mvw123/EMF_Sensor/EMF_Receiver.sch

## KiCad design EMF_Receiver.sch (2014-07-28, an earlier design)

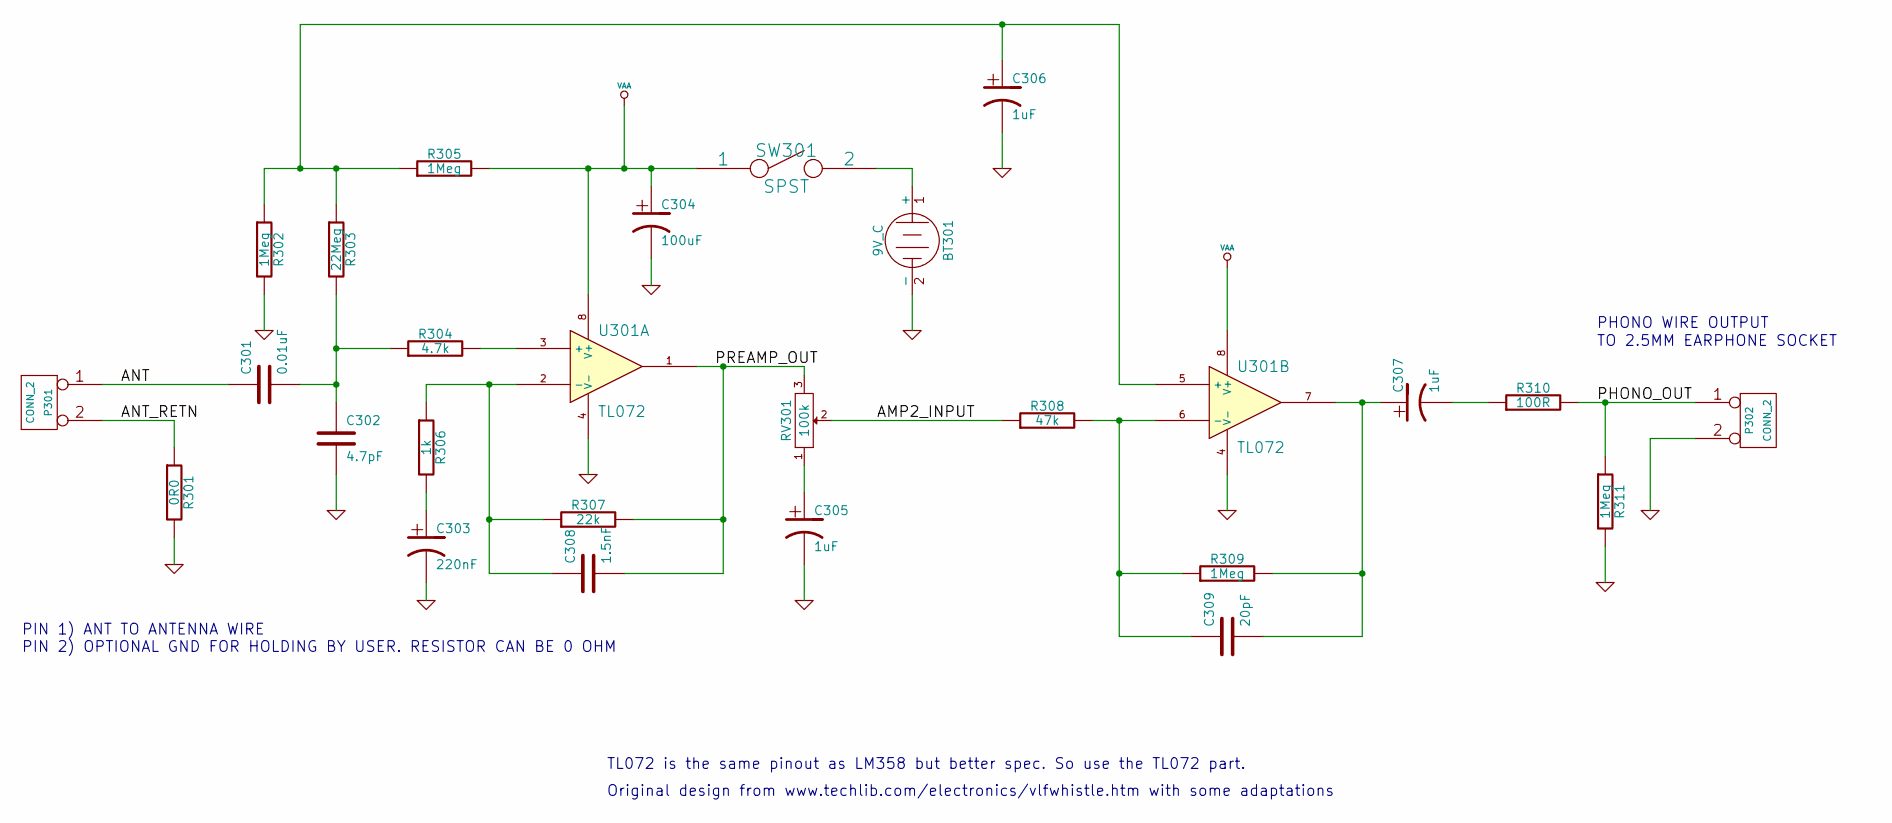
[picture p10: schematic EMF_Receiver.sch]

Parts:
BT301: 9V_C
C301: 0.01uF
C302: 4.7pF
C303: 220nF
C304: 100uF
C305, C306, C307: 1uF
C308: 1.5nF
C309: 20pF
P301, P302: CONN_2
R301: 0R0
R302, R305, R309, R311: 1Meg
R303: 22Meg
R304: 4.7k
R306: 1k
R307: 22k
R308: 47k
R310: 100R
RV301: 100k
SW301: SPST
U301: TL072

Connections:
AMP2_INPUT: R308.1, RV301.2
ANT: C301.1, P301.1
ANT_RETN: P301.2 (PM), R301.1
GND: BT301.2 (-), C302.2, C303.2, C304.2, C305.2, C306.2, P302.2 (PM), R301.2, R302.2, R311.2, U301.4 (V-)
unnamed: BT301.1 (+), SW301.2
unnamed: C301.2, C302.1, R303.2, R304.1
unnamed: C303.1, R306.2
unnamed: C305.1, RV301.1
unnamed: C306.1, R302.1, R303.1, R305.1, U301.5 (+)
unnamed: C307.1, C309.2, R309.2, U301.7
unnamed: C307.2, R310.1
unnamed: C308.1, R306.1, R307.1, U301.2 (-)
unnamed: C309.1, R308.2, R309.1, U301.6 (-)
unnamed: R304.2, U301.3 (+)
PHONO_OUT: P302.1, R310.2, R311.1
PREAMP_OUT: C308.2, R307.2, RV301.3, U301.1
VAA: C304.1, R305.2, SW301.1, U301.8 (V+)

Notes on the sheet:
PHONO WIRE OUTPUT
TO 2.5MM EARPHONE SOCKET
PIN 1) ANT TO ANTENNA WIRE PIN 2) OPTIONAL GND FOR HOLDING BY USER. RESISTOR CAN BE 0 OHM
Original design from www.techlib.com/electronics/vlfwhistle.htm with some adaptations
TL072 is the same pinout as LM358 but better spec. So use the TL072 part.
