mvw123/EMF_Sensor/RelaxationOscillator.sch

## KiCad design RelaxationOscillator.sch (2014-07-28, an earlier design)

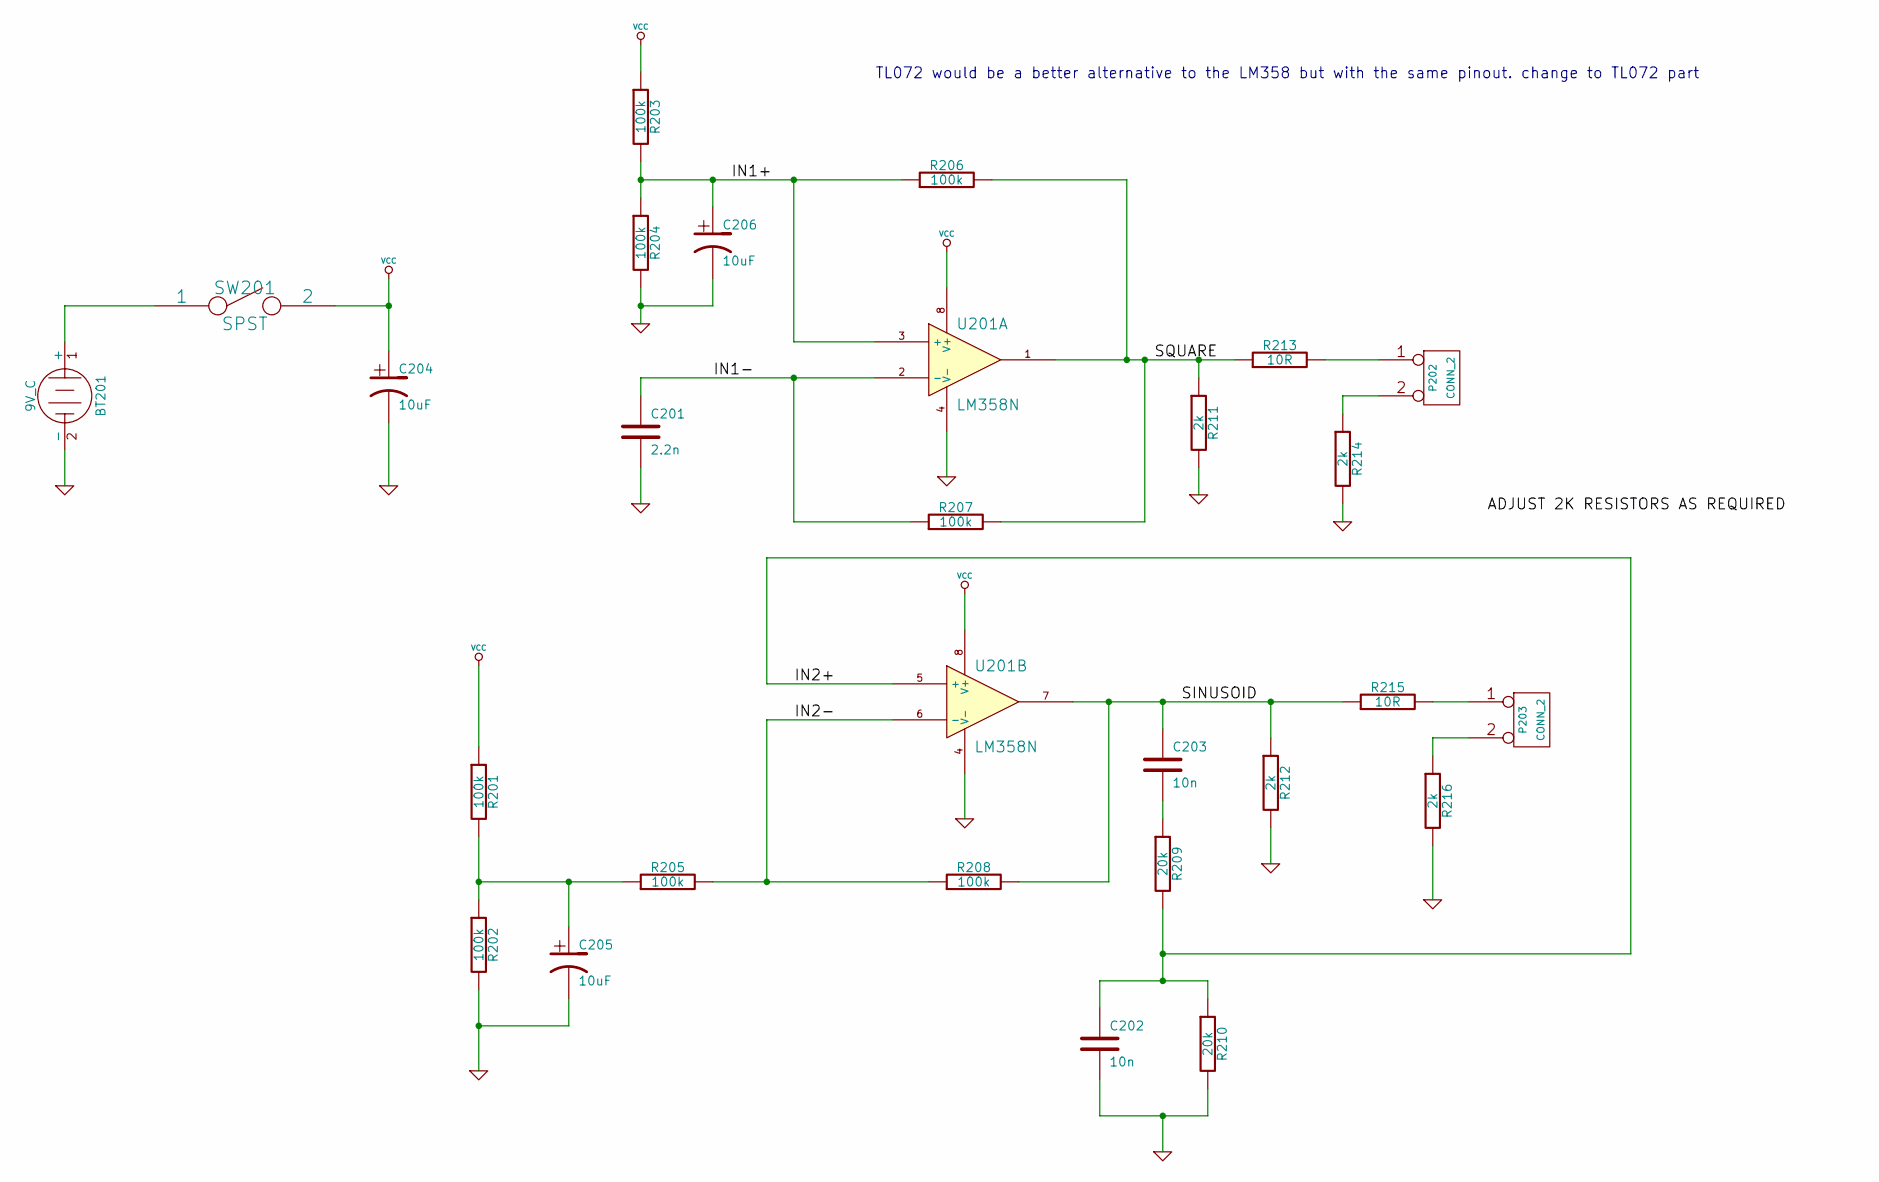
[picture p11: schematic RelaxationOscillator.sch]

Parts:
BT201: 9V_C
C201: 2.2n
C202, C203: 10n
C204, C205, C206: 10uF
P202, P203: CONN_2
R201, R202, R203, R204, R205, R206, R207, R208: 100k
R209, R210: 20k
R211, R212, R214, R216: 2k
R213, R215: 10R
SW201: SPST
U201: LM358N

Connections:
GND: BT201.2 (-), C201.2, C202.2, C204.2, C205.2, C206.2, R202.2, R204.2, R210.2, R211.2, R212.2, R214.2, R216.2, U201.4 (V-)
IN1+: C206.1, R203.2, R204.1, R206.1, U201.3 (+)
IN1-: C201.1, R207.1, U201.2 (-)
IN2+: C202.1, R209.2, R210.1, U201.5 (+)
IN2-: R205.2, R208.1, U201.6 (-)
unnamed: BT201.1 (+), SW201.1
unnamed: C203.2, R209.1
unnamed: C205.1, R201.2, R202.1, R205.1
unnamed: P202.1, R213.2
unnamed: P202.2 (PM), R214.1
unnamed: P203.1, R215.2
unnamed: P203.2 (PM), R216.1
SINUSOID: C203.1, R208.2, R212.1, R215.1, U201.7
SQUARE: R206.2, R207.2, R211.1, R213.1, U201.1
VCC: C204.1, R201.1, R203.1, SW201.2, U201.8 (V+)

Notes on the sheet:
TL072 would be a better alternative to the LM358 but with the same pinout. change to TL072 part
